antoine163/Mini-Light/Meca/control_box/prusa-slicer/control_box-control_box.3mf

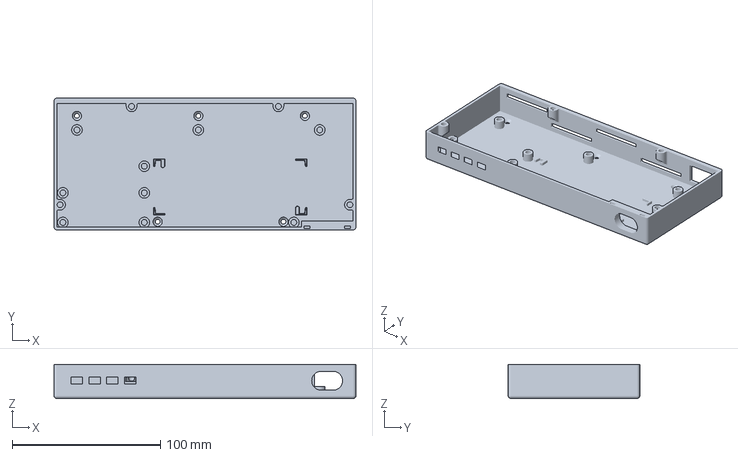
[picture p27: CAD file, 2022-03-13]
Meca/control_box/prusa-slicer/control_box-control_box.3mf
204.0 x 89.0 x 23.0 mm
