antoine163/Mini-Light/Meca/control_box/stl/control_box-Fix2_Power_Supply.stl

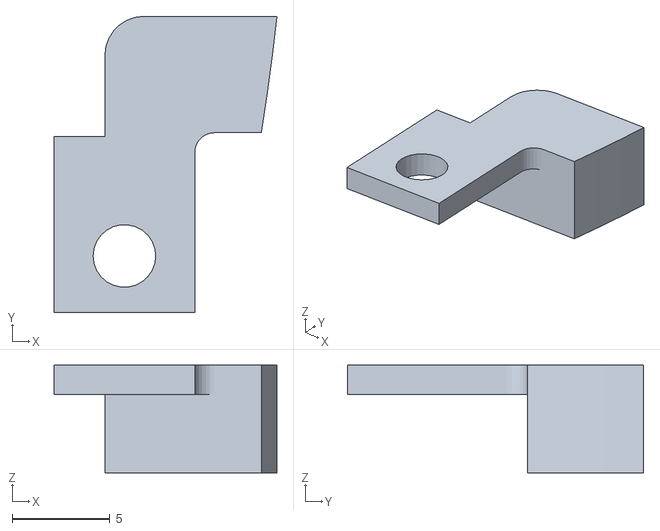
[picture p28: CAD file, 2022-03-13]
Meca/control_box/stl/control_box-Fix2_Power_Supply.stl
11.4 x 15.2 x 5.50
