antoine163/Mini-Light/Meca/light_support_for_prusa/mini_light.step

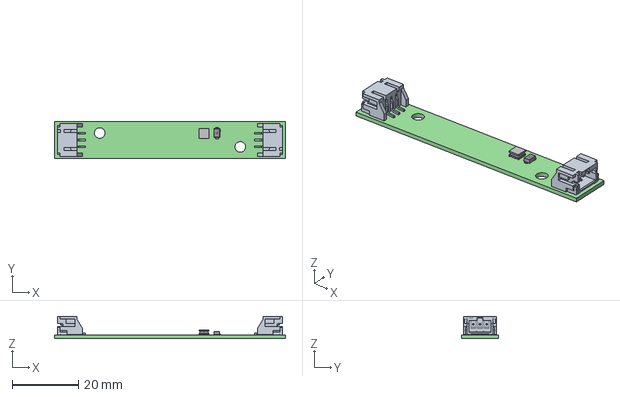
[picture p29: CAD file, 2022-07-01]
Meca/light_support_for_prusa/mini_light.step
70.0 x 11.2 x 6.75 mm
mini_light PCB
