antoine163/Mini-Light/Meca/control_box/prusa-slicer/control_box-SupPot.3mf

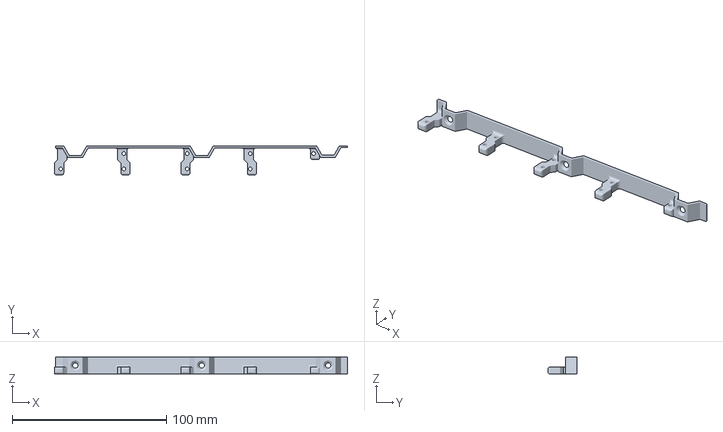
[picture p30: CAD file, 2022-03-13]
Meca/control_box/prusa-slicer/control_box-SupPot.3mf
190.0 x 19.0 x 11.0 mm
