antoine163/Mini-Light/Meca/control_box/prusa-slicer/control_box-Fix_Power_Supply.3mf

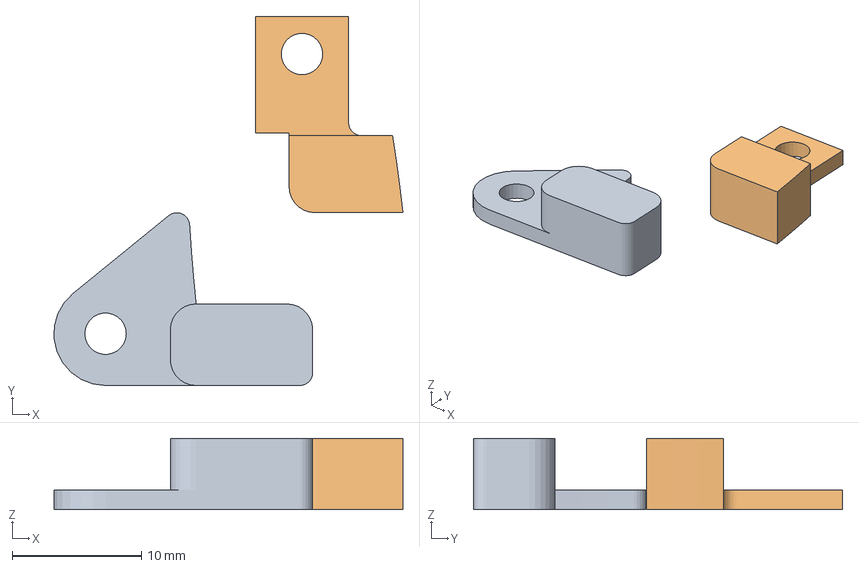
[picture p31: CAD file, 2022-03-13]
Meca/control_box/prusa-slicer/control_box-Fix_Power_Supply.3mf
27.0 x 28.5 x 5.50 mm
control_box-Fix1_Power_Supply.stl
control_box-Fix2_Power_Supply.stl
